gchrizZz/RTW/01_Projektmanagement/Structural Model Mohne.pdf

Motoren

MPU/ Gyroskope/
Ultraschallsensor/
Kamera

Arduino Uno /
Rasbery Pi

Servoelemente
(Vorwärtsbewegung) Motorleistung
steuert | Kommuniziert
kontrolliert | überwacht | kontrolliert
