gchrizZz/RTW/01_Projektmanagement/Aufgabenstellung_Uebung1.pdf

# Mars Explorer

Thomas Schmiedinger
thomas.schmiedinger@fh-kufstein.ac.at
13. Januar 2018

1

## 1 Embedded Systems UE - Raspberry Pi und Kameramodul

Als Teil des Projekts Mars Explorer soll im Rahmen der LV Embedded Systems UE die Hardware-Basis, der Raspberry Pi 3 und das Kameramodul, kennenge-
lernt werden. Der Raspberry Pi bildet das Ruckgrat f ¨ | ur den Mars Explorer. Aus ¨
diesem Grund beschäftigt sich die erste Einheit ausschließlich mit den Basics des Systems.

### 1.1 Ziel der Ubung ¨

Ziel der Ubung ist die erfolgreiche Inbetriebnahme des Raspberry Pi 3. Dazu ¨ zählt der Hardware-Aufbau, die Installation eines Betriebssystems, Anbindung an das Internet und ein abschließendes Systemupdate. Ein weiteres Ziel der
Ubung ist die Inbetriebnahme des Kameramoduls. Dazu z ¨ | ählt der physische
Anschluss an den Raspberry Pi, die Konfiguration des Raspberry Pis sowie die Ansteuerung der Kamera mit einem Python-Programm.

### 1.2 Beurteilung der Ubung ¨

Mithilfe des Raspberry Pis und der Kamera soll ein Bild sowie eine kurze Videosequenz (ca. 5sec) aufgenommen und gespeichert werden. Beide Files werden als zip-Ordner in Moodle hochgeladen.

### 1.3 Aufgabenstellung

### 1.3.1 Aufbau der Hardware

1. Entfernen Sie die Schutzfolie auf beiden Seiten der Plexiglas Grundplatte.
2. Offnen Sie die Box des Raspberry Pi 3 (Achten Sie auf die beigelegte ¨ SD-Karte).
3. Setzen Sie die SD Karte in den Raspberry Pi 3 ein.

2

4. Montieren Sie den Raspberry Pi auf der Grundplatte. Verwenden Sie dazu die kleinen der beigelegten Schrauben.
5. Befestigen Sie das Breadboard auf der Grundplatte.
6. Schließen Sie USB Tastatur und USB Maus an den Raspberry Pi 3 an. Verwenden Sie dazu die Eingabegeräte an den Stand-PCs.
7. Schließen Sie das HDMI Kabel an den Raspberry Pi 3 an.
8. Schließen Sie das USB Netzteil am Raspberry Pi 3 an.
9. Verbinden Sie das USB Netzteil mit der Stromversorgung.

### 1.3.2 Installation des Betriebssystems

Nachfolgend sind grob die einzelnen Schritte zur Installation angefuhrt. Eine ¨
gute Quelle fur weitere Informationen ist auf der Homepage der ¨ | Raspberry
Foundation (https://www.raspberrypi.org/) zu finden. Beim ersten Hochfahren mit NOOBS erscheint ein Auswahlbildschirm. Hier können Sie auswählen, welches Betriebssystem Sie auf dem Raspberry Pi 3 installieren wollen.
1. Wählen Sie das Betriebssystem Raspbian. (http://raspbian.org/) Fur das weitere Projekt steht ¨ Ihnen die Wahl des Betriebssystems fur den Raspberry Pi 3 frei. Eine gute ¨
Ubersicht zu den unterschiedlichen Systemen finden Sie ¨ | hier. (https://raspberrypi.stackexchange.com/questions/534/definitive-list-of-operating-systems)
2. Das Betriebssystem wird installiert.
3. Stellen Sie eine Internetverbindung her. Verbinden Sie dazu das Netzwerkkabel mit dem Raspberry Pi oder stellen Sie via Wlan eine Verbindung mit dem Internet her (Wifi-Netzwerk FH-Gast).
4. Nach erfolgter Installation wird das Betriebssystem auf den aktuellen Stand gebracht.
5. Offnen Sie das Terminal. ¨
6. Fuhren Sie ein Update aus. Geben Sie den Befehl ¨ | sudo apt-get update
in das Terminal ein und bestätigen Sie mit Enter.
7. Fuhren Sie nun ein Upgrade durch. Der Befehl lautet ¨ | sudo apt-get dist-upgrade.
Das System ist nun auf aktuellen Stand.

3

### 1.3.3 Kamera anschließen

1. Fahren Sie den Rapsberry Pi 3 herunter und kappen Sie die Verbindung zur Stromversorgung.
2. Verbinden Sie die Kamera mit dem Raspberry Pi 3.
3. Starten Sie den Raspberry Pi 3.
4. Offnen Sie das Programm ¨ | Raspberry Pi Configuration Tool. Sie fin-
den dieses im Menupunkt ¨ | Preferences.
5. Aktivieren Sie die Kamera.
6. Starten Sie den Raspberry Pi 3 neu.

### 1.3.4 Kameravorschau starten

1. Starten Sie unter Programming das Programm Python 3.
2. Erstellen Sie eine neue Datei und speichern Sie diese.
3. Erstellen Sie folgenden Code:

from picamera import PiCamera
from time import s l e e p

camera = PiCamera ( )

camera . s t a r t p r e v i e w ( ) s l e e p ( 1 0 )
camera . s t o p p r e vi e w ( )
4. Speichern Sie die Datei und starten Sie das Programm (F5).
5. Sollte das Bild auf dem Kopf stehen, können Sie die Ausrichtung des Bildes ändern. Verwenden Sie dazu folgenden Code:

from picamera import PiCamera
from time import s l e e p

camera = PiCamera ( )

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

4

Das Bild kann um 90, 180 oder 270 Grad gedreht werden.

6. Testen sie die Transparenz Einstellungen der Kamera. Verwenden Sie dazu folgenden Code:

from picamera import PiCamera
from time import s l e e p

camera = PiCamera ( )

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

Der Wert fur alpha bestimmt die Transparenz und kann zwischen 0 und ¨ 255 geändert werden.

### 1.3.5 Bild aufnehmen und abspeichern

1. Nehmen Sie mit der Kamera ein Bild auf und speichern Sie diese ab.
2. Fuhren Sie dazu folgendes Programm aus: ¨

from picamera import PiCamera
from time import s l e e p

camera = PiCamera ( )

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

Die Wartezeit von 2 Sekunden ist notwendig, damit sich der Kamerasensor auf die Lichtverhältnisse einstellen kann.

3. Offnen Sie das Foto. ¨
4. Adaptieren Sie das Programm um 5 Bilder in Serie aufzunehmen.

### 1.3.6 Video aufnehmen und abspeichern

1. Nehmen Sie mit der Kamera ein kurzes Video auf und speichern Sie diese ab.

5

2. Fuhren Sie dazu folgendes Programm aus: ¨

from picamera import PiCamera from time import s l e e p

camera = PiCamera ( )

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

6

## 2 Hinweise

### 2.1 Remote-Zugriff auf Raspberry Pi

Es besteht die Möglichkeit, mittles SSH Verbindung auf den Raspberry Pi zuzugreifen. Eine Anleitung dazu finden auf der Homepage der Raspberry Pi Foundation. (https://www.raspberrypi.org/documentation/remote-access/ssh/) Dies funktioniert nur nach Installation der Betriebssoftware.

Nachteil der PuTTY Lösung ist, dass es einen Zugriff auf die Kommandozeile gibt. Um auch die Oberfläche zu starten, folgen Sie der Anleitung. (http://42bots.com/tutorials/access-raspberry-pi-terminal-and-desktop-remotely-with-ssh-and-vnc/) Prinzipiell handelt es sich dabei um eine Erweiterung der SSH Anbindung um somit auch den Desktop des Raspberry Pis via remote anzeigen zu können.

Prinzipiell ist eine SSH-Anbindung ausreichend. Mithilfe von Kommandozeilen Befehlen ist es möglich, Dateien zu verwalten (z.B. Ordnerstruktur erstellen, Dateien verschieben etc.). Einen guten Uberblick der meisten Linux Befehle ¨ finden Sie hier. (https://www.raspberrypi.org/documentation/linux/usage/commands.md)

### 2.2 Ansteuerung von Sensoren und Aktoren - GPIO

Der Raspberry Pi 3 besitzt ein Interface uber welchem mit Sensoren und Aktoren ¨ kommuniziert werden kann. Die GPIO Pins besitzen unterschiedliche Funktionalitäten. Die Ansteuerung der Pins ist in diesem Tutorial (https://tutorials-raspberrypi.de/raspberry-pi-gpio-erklaerung-beginner-programmierung-lernen/) gut erklärt. Fur die ¨ vorhandene Sensoren finden Sie hier (http://sensorkit.joy-it.net/index.php?title=Hauptseite) Beispielprogramme.

### 2.3 Unified Modelling Language fur Raspberry Pi ¨

Mit folgenden Befehl in der Kommandozeile können Sie Umbrella auf Ihrem Raspberry Pi 3 installieren:

ssudo apt-get install umbrello

7

### 2.4 Informationen zur Picamera

Die Software der Kamerasteuerung bietet weitere Funktionalität hinsichtlich
Aufnahmemodi. Weiterfuhrende Informationen dazu finden Sie auf auf ¨ | Picame-
ra. (https://picamera.readthedocs.io/en/release-1.13/)

### 2.5 Informationen zu Objekterkennung

Spannend wird das Projekt hinsichtlich Objekterkennung. Der Raspberry Pi 3 in Kombination mit einer Kamera bietet die Möglichkeit, dies umzusetzen. Eine Möglichkeit dazu, bietet die Umgebung OpenCV. (https://opencv.org/) Von OpenCV finden sich einige Tutorials im Netz, wie auch dieses (https://docs.opencv.org/master/d2/d64/tutorial_table_of_content_objdetect.html) in welchen die Erkennung von Objekten gezeigt wird. Informationen dazu finden Sie auf der Homepage von
pyimagesearch. (https://www.pyimagesearch.com/start-here-learn-computer-vision-opencv/) Eine Installationsanleitung fur OpenCV findet sich ¨ | hier. (https://tutorials-raspberrypi.de/opencv-auf-dem-raspberry-pi-installieren/)
Eine weitere Inspirationsquelle fur Objekterkennung bietet die Freeware ¨ | YOLO. (https://pjreddie.com/darknet/yolo/)
Die Funktionalität dieses Programm wurde von Joseph Redmon im Rahmen eines TED-Talks (https://www.ted.com/talks/joseph_redmon_how_a_computer_learns_to_recognize_objects_instantly/up-next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) eindrucksvoll demonstriert.

8
