gchrizZz/RTW/04_Elektrik/Elektrik.pptx

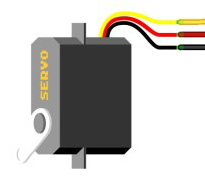
[picture p71: figure]
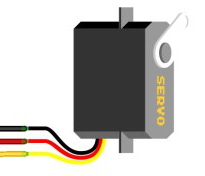
[picture p72: figure]
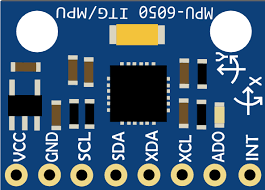
[picture p73: figure]
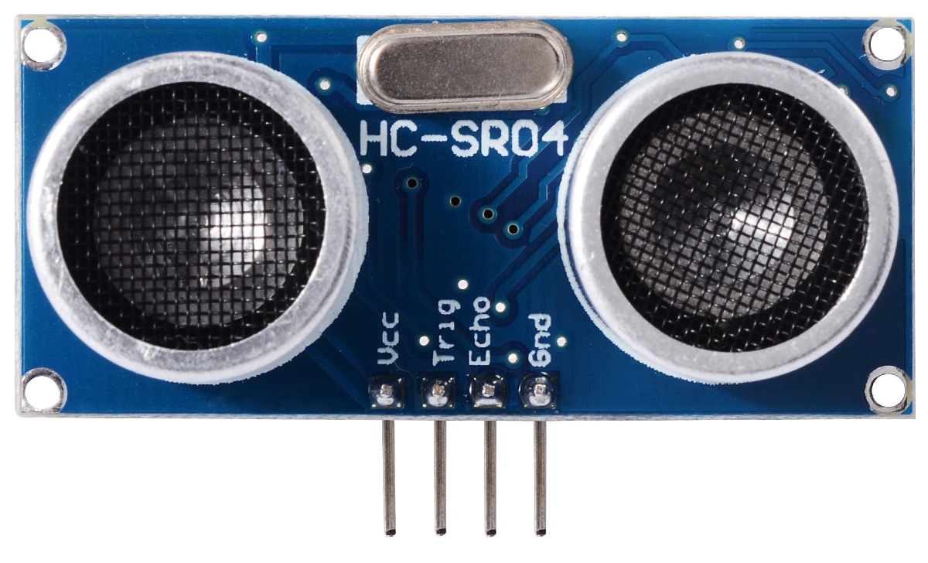
[picture p74: figure]
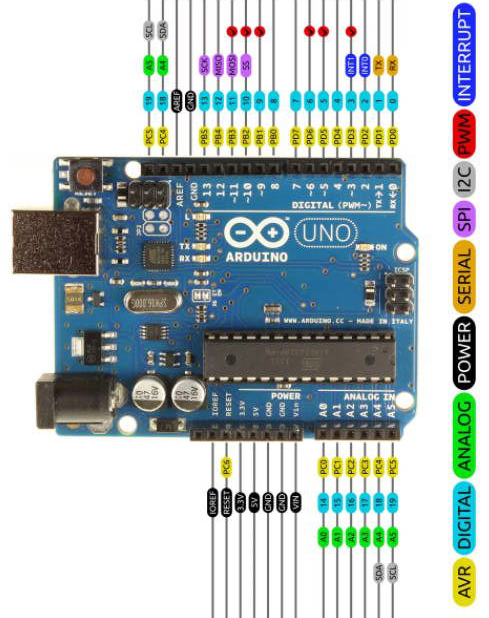
[picture p75: figure]
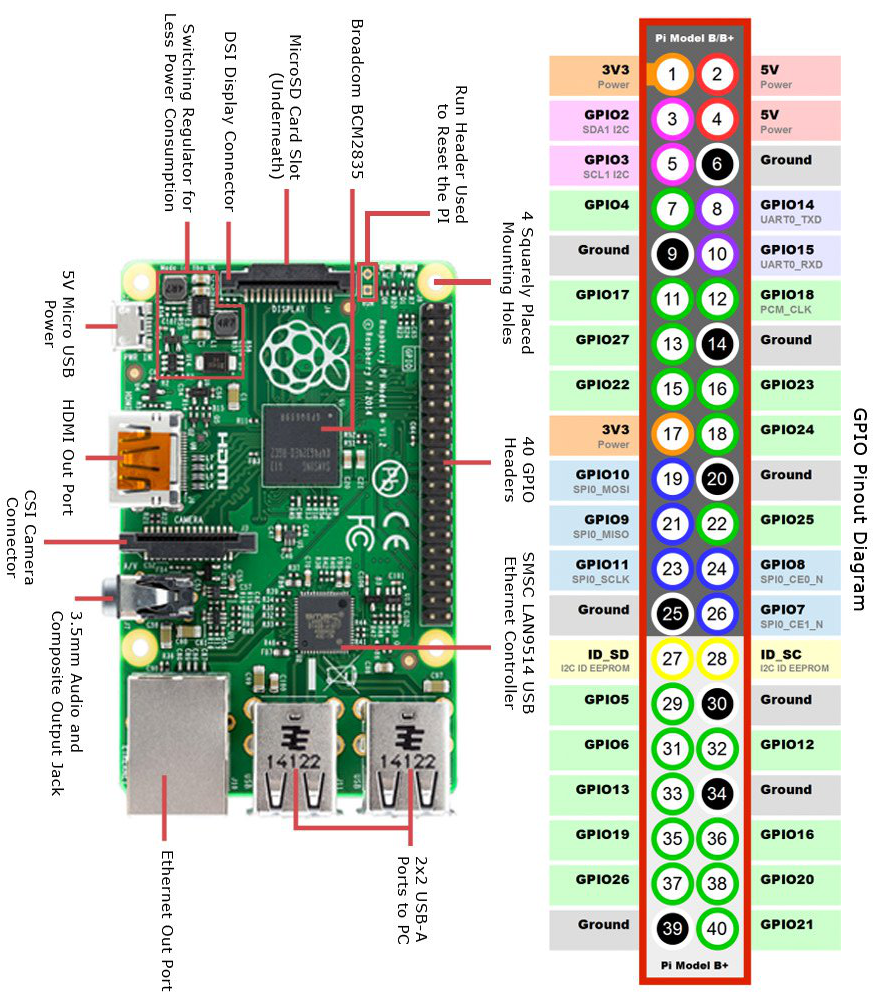
[picture p76: figure]
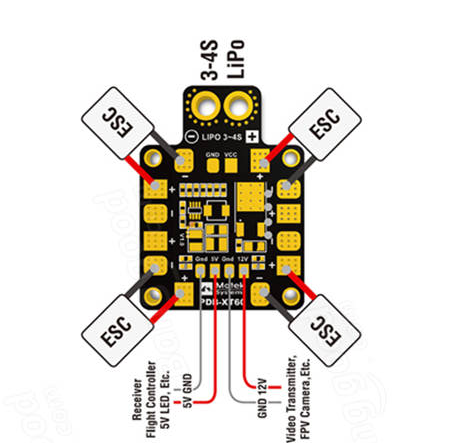
[picture p77: figure]
