gchrizZz/RTW/01_Projektmanagement/Assignment 5 - Project Managements Methods - ACC.pptx

## Smart Produkt Solutions Assignment 5 – Project Management Methods SPS bbM, WS 2017/18

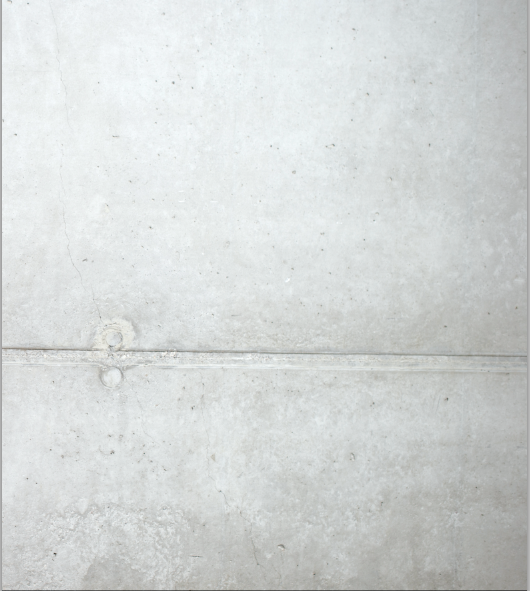
[picture p78: figure]
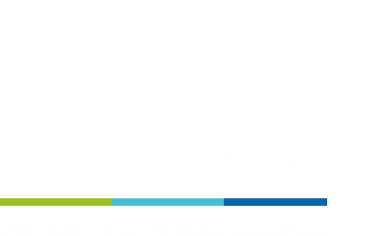
[picture p79: figure]

## Slide 2

Project Management Methods - "Mars Expedition"

Assignment 5 – Project Management Methods
Planning vehicle for „Mars Expedition“
Anna Duregger,
Christoph Jungwirth,
Christian Gruber

## Project use case

Distribution of roles
  - Project manager and deputy project manager
  - Head of construction
  - Head of computer engineering
  - Head of electronic engineering
  - Decision maker
  - Responsibility

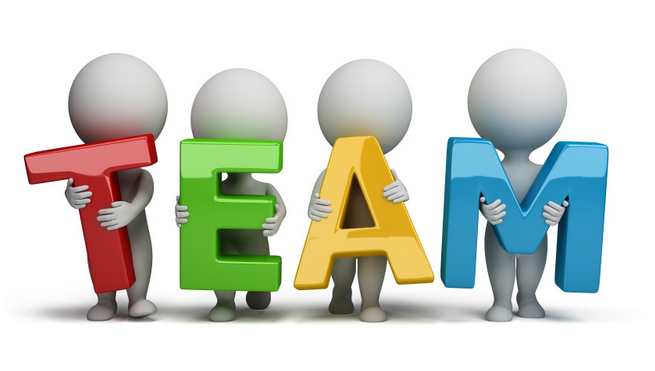
[picture p80: figure]

Quelle: http://www.flensburger-budo-club.de/attachments/Image/team.jpg?template=generic

## Project use case

Phase planning
  - Conception phase
  - Define and Planning phase
  - Execution Phase
  - Closing Phase (Mars Landing)
  - Structure
  - Set up activities
  - Work step by step

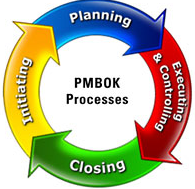
[picture p81: figure]

Source: http://www.mpmm.com/images/pmbok-processes.jpg

## Project use case

Milestones
  - 1st: Structure, basic concept, distribution of roles
  - 2nd: Prototyping of our Mohne
  - 3rd: Optimization for our finalisation phase
  - Control project progression
  - Relief project planning

Quelle: http://laoblogger.com/images/milestone-clipart-10.jpg

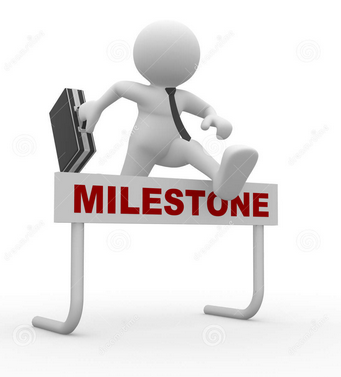
[picture p82: figure]

## Project at a glance

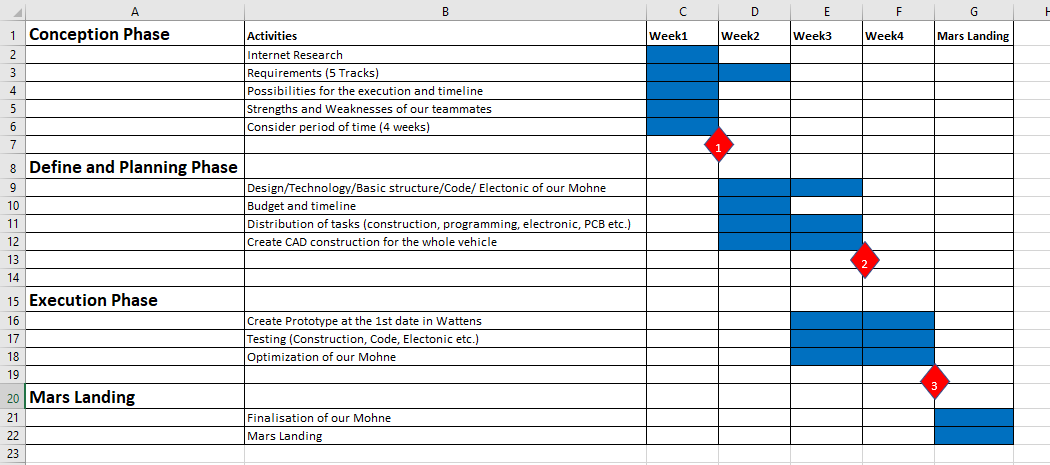
[picture p83: figure]

## Project supporting tools

GitHub
- Used as a Collaboration Tool for the Project
- Separate the Tasks regarding the project phases
- In addition to the project plan → more clearly & detailed
Templates (based on Excel)
- Project owner Requirements (Tasks for the Robot)
- Team Member Structure (Who is Who?)
- Risk analysis (for the Robot)
- Technical Requirements (Construction)

## Risk evaluation of the Project

- Evaluating potential Risks of the Project regarding the customer requirements
- Create controlling tools for the detected risks
- Finding solutions for the come out risks
- Discriminate between project risks and standard risks

Standard risks | Project risks
Competing goals | Technical Issues
Project environment | Time Table / Delivery Schedule
Stakeholder | Customer Requiremants

## Traditional vs. Agile Methods

Traditional project management:
What‘s the overall plan and conditions - in our Project?

- Specification list
- Risk analysis
- Define goal

Initiation

- Work off Workpackages
- Document the progress

Execution

- Work off Workpackages
- Document the progress

Closing

Planning

- Milestone plan
- Determine resources
- Define work packages

Monitoring & Control

- Control scope, progress, cost
- Readjust the project planning

## Traditional vs. Agile Methods

Traditional project management:
Goal of traditional project management - in our project?

TIME

COST

In our case:

QUALITY

QUALITY? – We will see

TIME

COST=Budget

SCOPE

SCOPE

## Traditional vs. Agile Methods

Agile project management:
Agile development in our project?

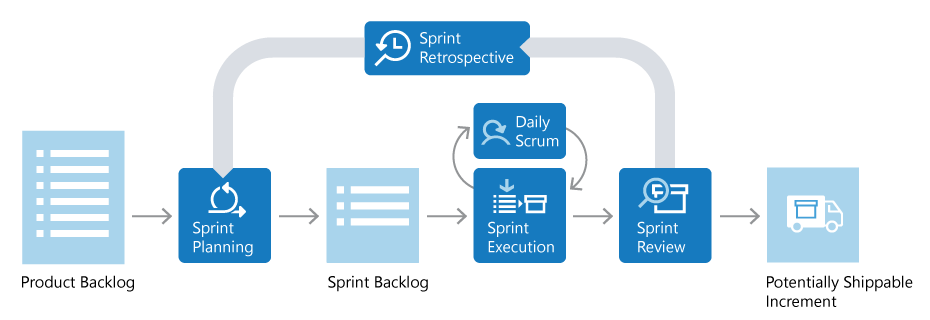
[picture p84: figure]

Daily communication via whatsapp and github
(for CAD and sourcecode)

Our „To Do“ on github

„In progress“ on github

Review with the complete team over all accomplished workpackages

Source: https://www.visualstudio.com/de/learn/what-is-scrum/?rr=https%3A%2F%2Fwww.google.de%2F

## Traditional vs. Agile Methods

Conclusion:

Traditional | Agile
Formal and hierarchical – straight forward | Informal, decisions are made in the entire team – loops possible
Anticipation: No changes during the project | Adaption: Embraces changes
Early planning and complete overview is key to success of the project | Fest reaction and adoption during the project is key to success

Overall planning

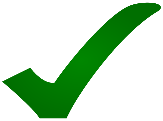
[picture p85: figure]

Development
