gchrizZz/RTW/01_Projektmanagement/Assignment 5 - Project Managements Methods_Christoph und Anna.pptx

## Smart Produkts & Solutions Assignment 5 – Project Management Methods SPS bbM, WS 2017/18


## Slide 2

Project Management Methods - "Mars Expedition"

HANDOUT NICHT VERGESSEN
Assignment 5 – Project Management Methods
Planning vehicle for „Mars Expedition“
Anna Duregger,
Christoph Jungwirth,
Christian Gruber

## Agenda

1. Project use case
2. Project at a glance
3. Project supporting tools
4. Risk evaluation of the Project
5. Traditional vs. Agil Methods

## Project use case

Phase planning
  - Conception phase
  - Define and Planning phase
  - Execution Phase
  - Mars Landing
  - Structure
  - Set up activities
  - Work step by step

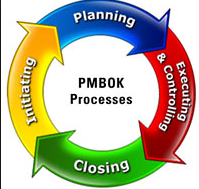
[picture p87: figure]

## Project use case

Milestones
  - 1st: structure, basic concept, distribution of roles
  - 2nd: prototyping our Mohne
  - 3rd: optimization for our finalisation phase
  - Control project progession
  - Relief project planning

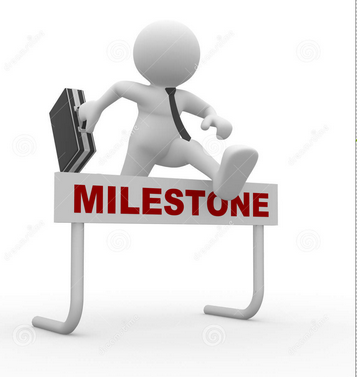
[picture p88: figure]

## Slide 6

Distribution of roles
  - Project Manager and Deputy Project Manager
  - Head of Construction
  - Head of computer engineering
  - Head of electronic engineering
  - Decision maker
  - Responsibility


## Project at a glance


## Project supporting tools

GitHub
- Used as a Collaboration Tool for the Project
- Separate the Tasks regarding the project phases
- In addition to the project plan → more clearly & detailed
Templates (based on Excel)
- Project owner Requirements (Tasks for the Robot)
- Team Member Structure (Who is Who?)
- Risk analysis (for the Robot)
- Technical Requirements (Construction)

## Risk evaluation of the Project

- Evaluating potential Risks of the Project regarding the customer requirements
- Create controlling tools for the detected risks
- Finding solutions for the come out risks
- Discriminate between project risks and standard risks

Standard risks | Project risks
Competing goals | Technical Issues
Project environment | Time Table / Delivery Schedule
Stakeholder | Customer Requiremants

## Traditional vs. Agil Methods
