gchrizZz/RTW/01_Projektmanagement/3dDrucker einstellungen.JPG

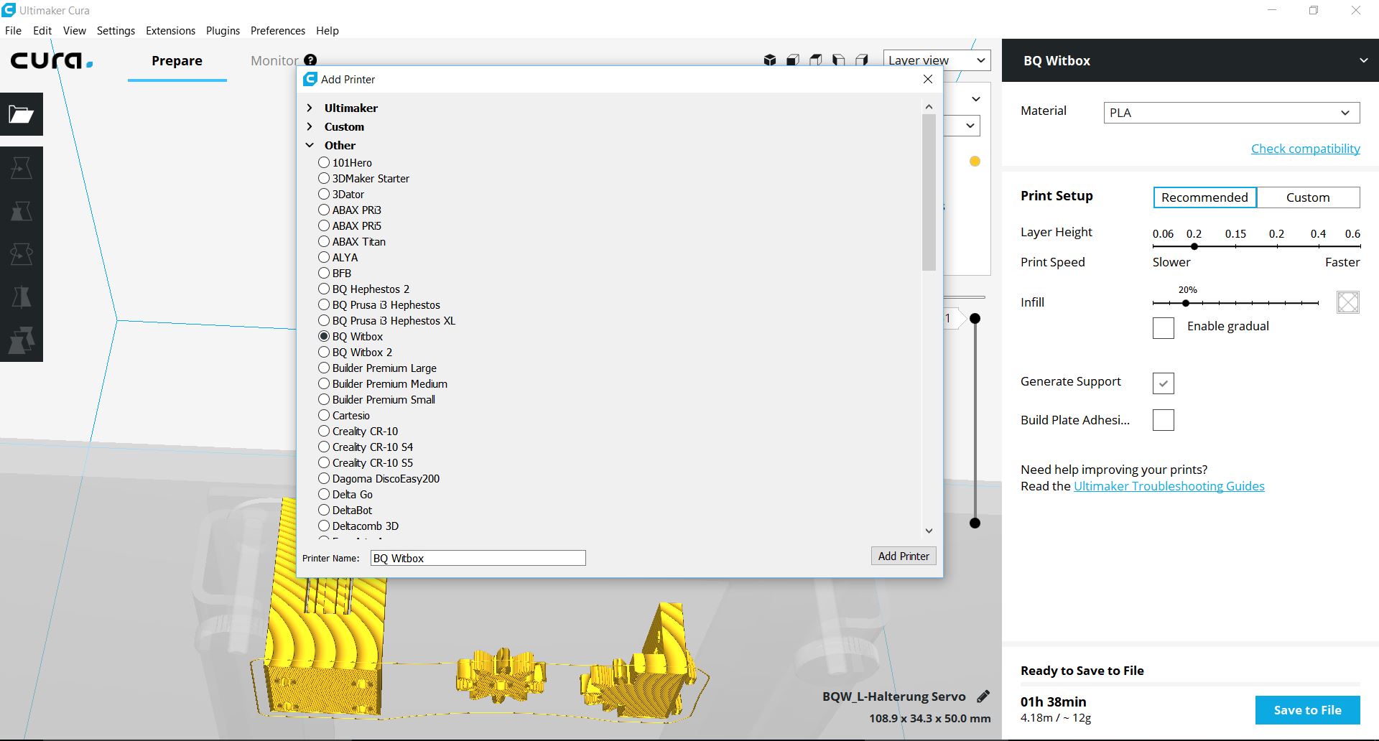
01_Projektmanagement/3dDrucker einstellungen.JPG
