gchrizZz/RTW/01_Projektmanagement/Bilder/IMG-20180123-WA0000.jpeg

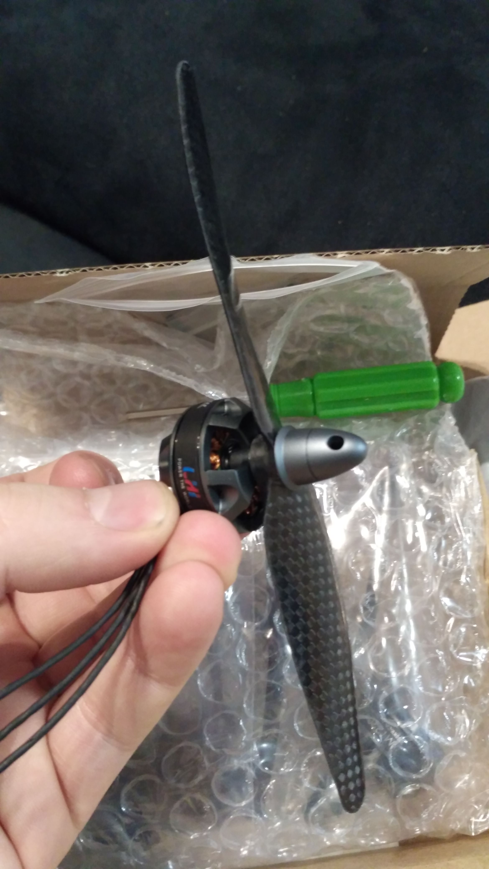
01_Projektmanagement/Bilder/IMG-20180123-WA0000.jpeg
