gchrizZz/RTW/01_Projektmanagement/Bilder/IMG-20180209-WA0006.jpeg

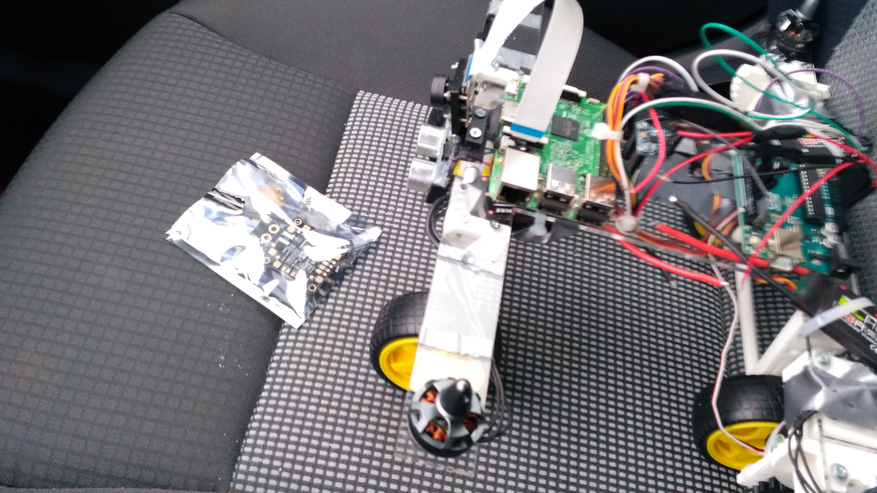
01_Projektmanagement/Bilder/IMG-20180209-WA0006.jpeg
