gchrizZz/RTW/01_Projektmanagement/Bilder/IMG-20180210-WA0005.jpg

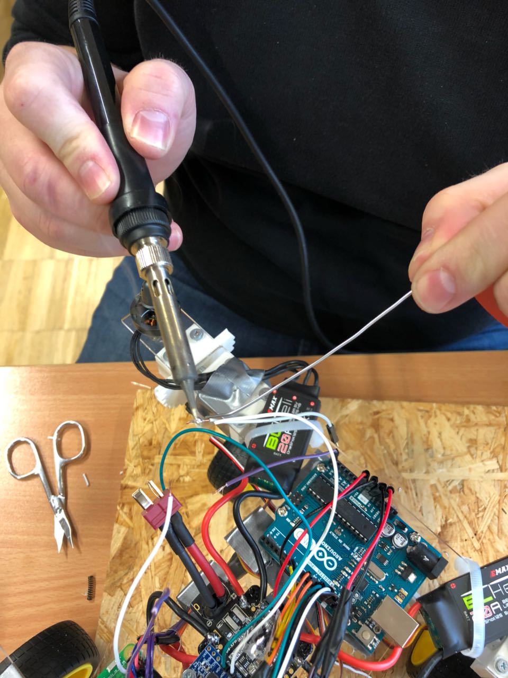
01_Projektmanagement/Bilder/IMG-20180210-WA0005.jpg
