gchrizZz/RTW/01_Projektmanagement/Bilder/IMG_20180129_200515.jpg

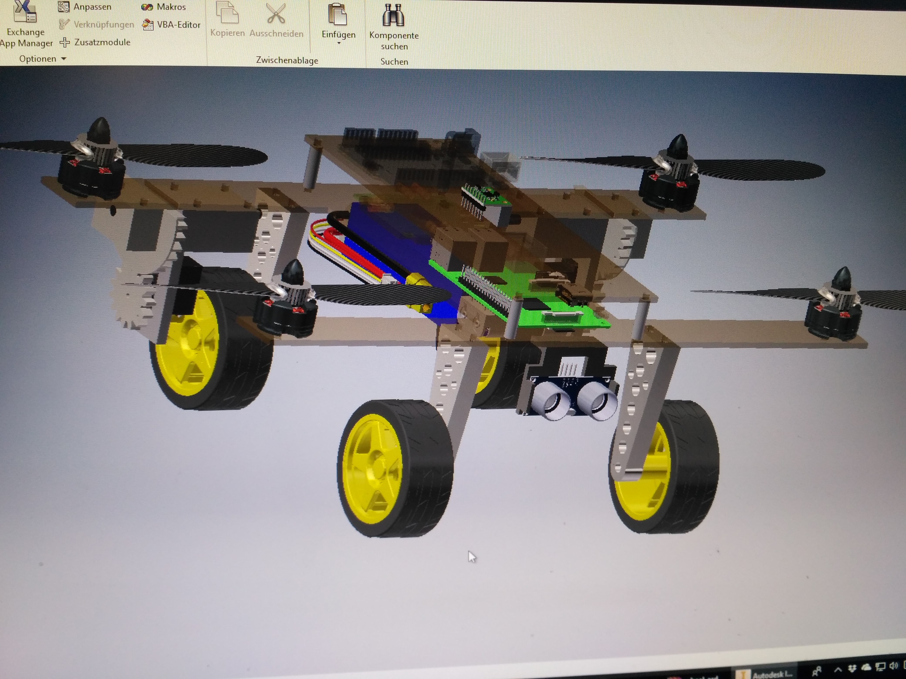
01_Projektmanagement/Bilder/IMG_20180129_200515.jpg
