gchrizZz/RTW/01_Projektmanagement/Bilder/PCB_monochromatic.jpeg

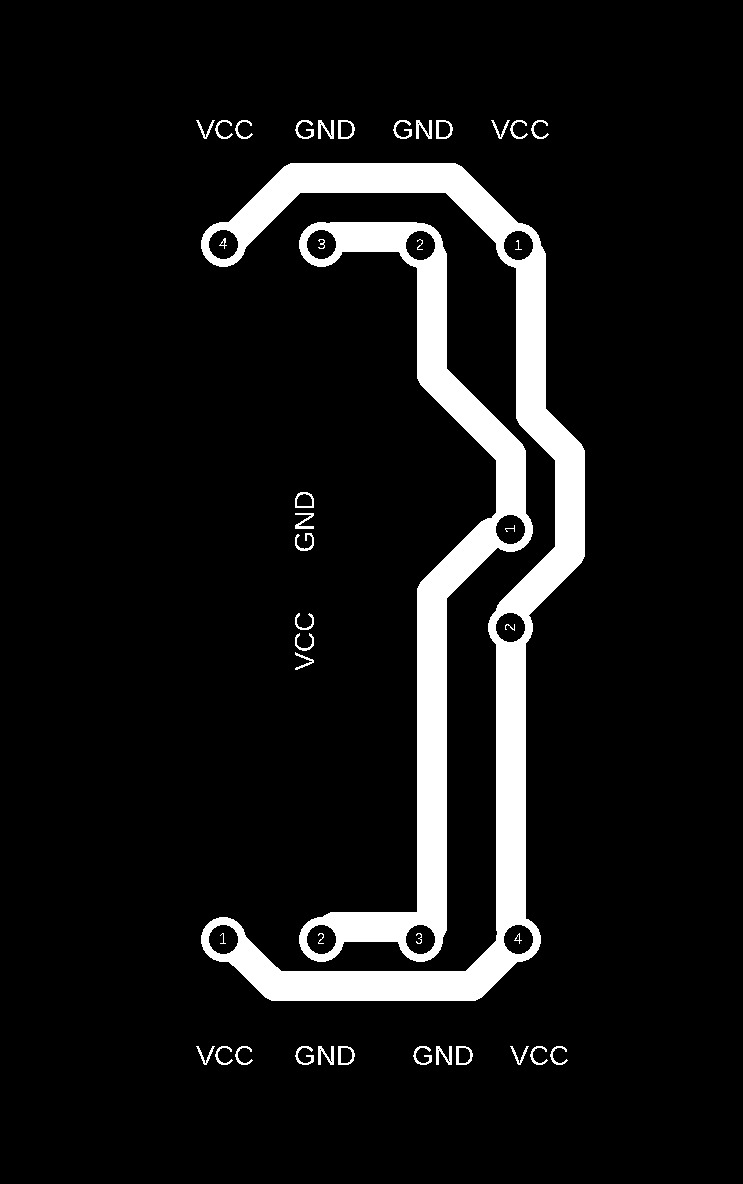
01_Projektmanagement/Bilder/PCB_monochromatic.jpeg
