gchrizZz/RTW/03_Konstruktion/2xAAA_ass.STEP

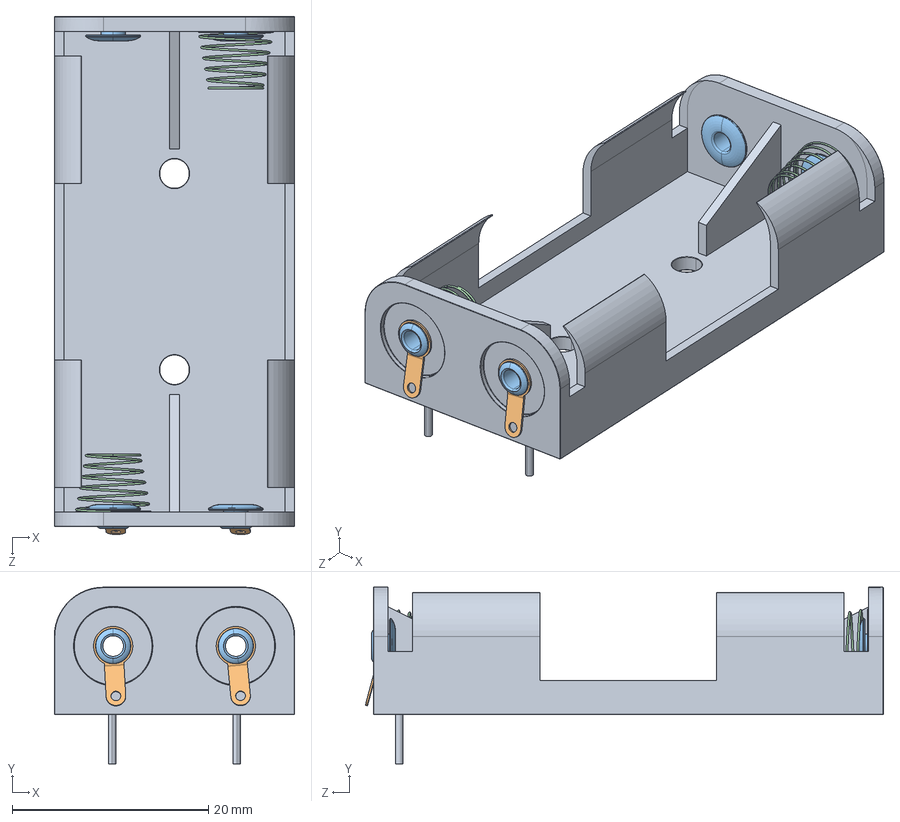
[picture p114: CAD file, 2018-01-30]
03_Konstruktion/2xAAA_ass.STEP
24.5 x 18.0 x 52.8 mm
battery holder 2 x AAA
wtyczka_Domyslna x 2
wstawka_Domyslna x 4
sprezyna_Domyslna x 2
