gchrizZz/RTW/03_Konstruktion/28-2-2013-002 - ESC 3-pin connector.SLDPRT

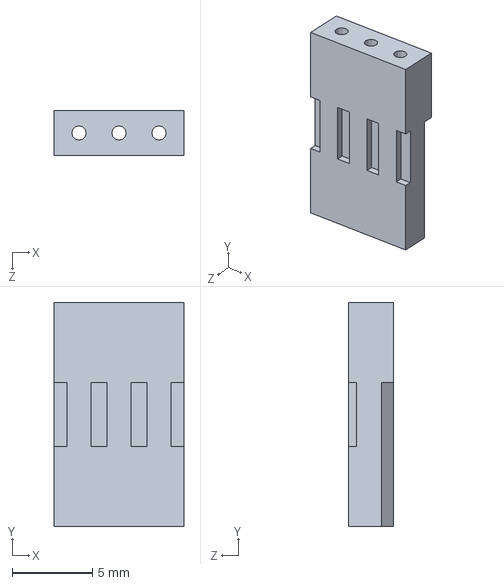
[picture p115: CAD file, 2018-01-30]
03_Konstruktion/28-2-2013-002 - ESC 3-pin connector.SLDPRT
8.10 x 14.0 x 2.80 mm
