gchrizZz/RTW/03_Konstruktion/Exporte/Abstandhalter_MPU.stl

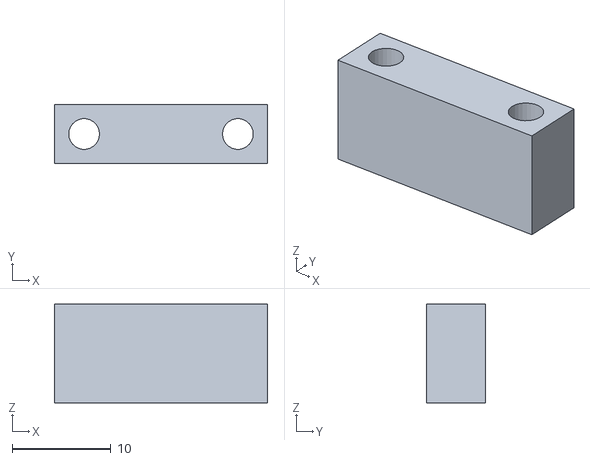
[picture p116: CAD file, 2018-01-30]
03_Konstruktion/Exporte/Abstandhalter_MPU.stl
21.6 x 6.00 x 10.0
