gchrizZz/RTW/03_Konstruktion/Exporte/kamera ut.stl

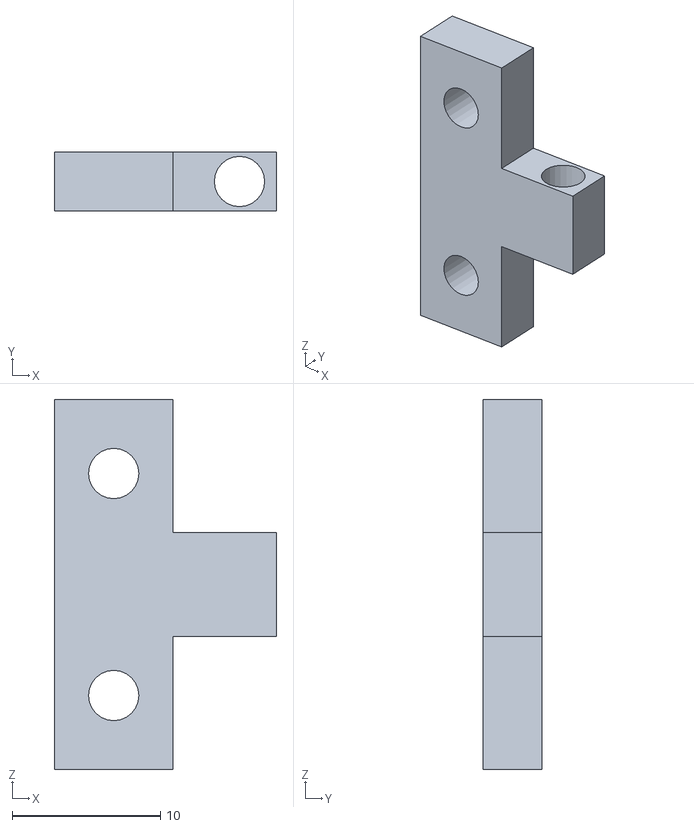
[picture p117: CAD file, 2018-01-30]
03_Konstruktion/Exporte/kamera ut.stl
15.0 x 4.00 x 25.0
