gchrizZz/RTW/03_Konstruktion/Resistor black.SLDPRT

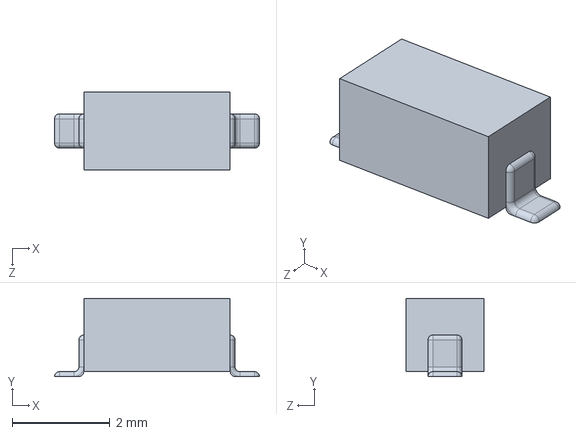
[picture p118: CAD file, 2018-01-20]
03_Konstruktion/Resistor black.SLDPRT
4.20 x 1.60 x 1.60 mm
