gchrizZz/RTW/03_Konstruktion/Base.SLDPRT

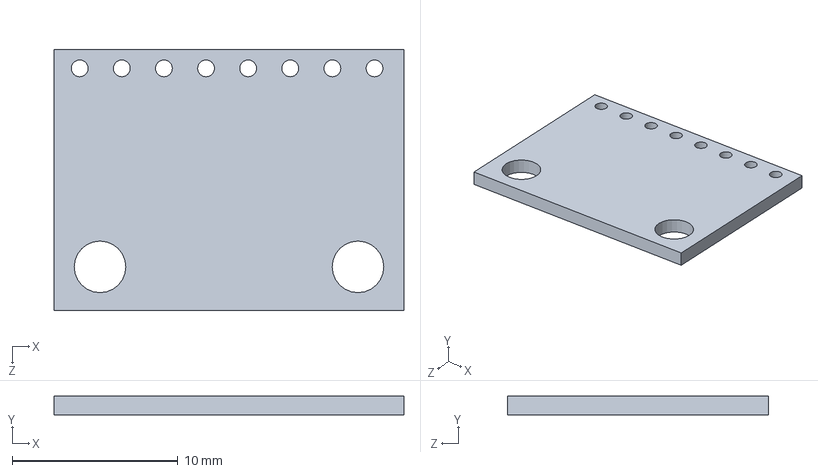
[picture p119: CAD file, 2018-01-20]
03_Konstruktion/Base.SLDPRT
21.1 x 1.14 x 15.7 mm
