gchrizZz/RTW/03_Konstruktion/MPU 6050 IMU.STEP

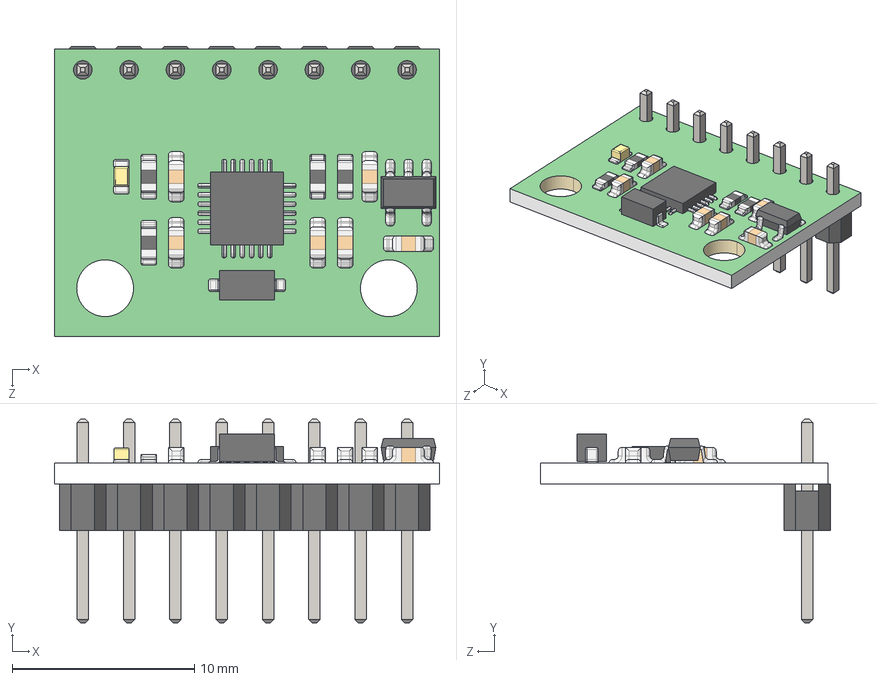
[picture p120: CAD file, 2018-01-20]
03_Konstruktion/MPU 6050 IMU.STEP
21.1 x 11.2 x 15.9 mm
Base
pin header x 8
sensor chip
S2NH chip
Resistor small x 6
Resistor small black x 4
Small LED
Resistor black
