gchrizZz/RTW/03_Konstruktion/Resistor small black.SLDPRT

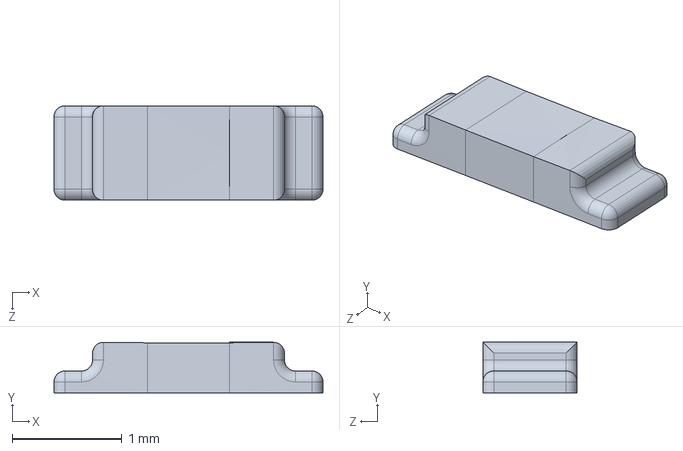
[picture p121: CAD file, 2018-01-20]
03_Konstruktion/Resistor small black.SLDPRT
2.45 x 0.46 x 0.86 mm
