gchrizZz/RTW/03_Konstruktion/sensor chip.SLDPRT

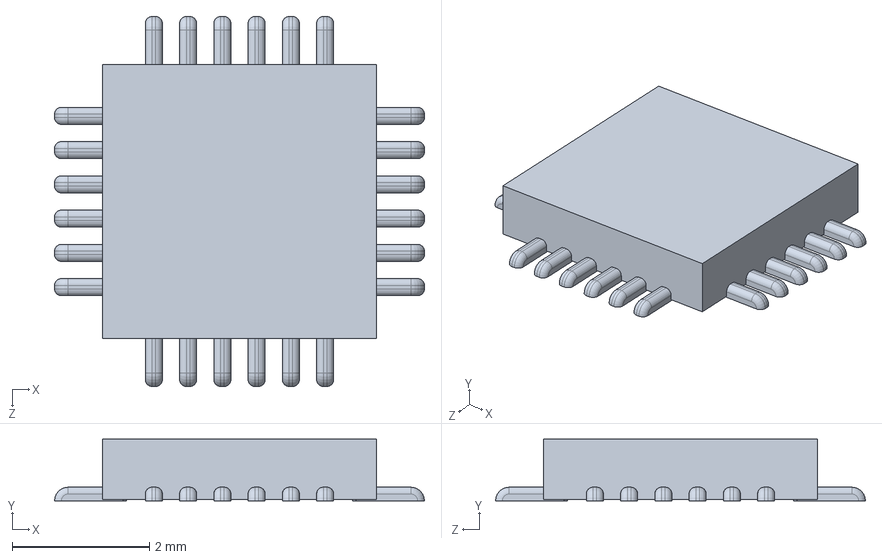
[picture p122: CAD file, 2018-01-20]
03_Konstruktion/sensor chip.SLDPRT
5.40 x 0.9 x 5.40 mm
