gchrizZz/RTW/03_Konstruktion/S2NH chip.SLDPRT

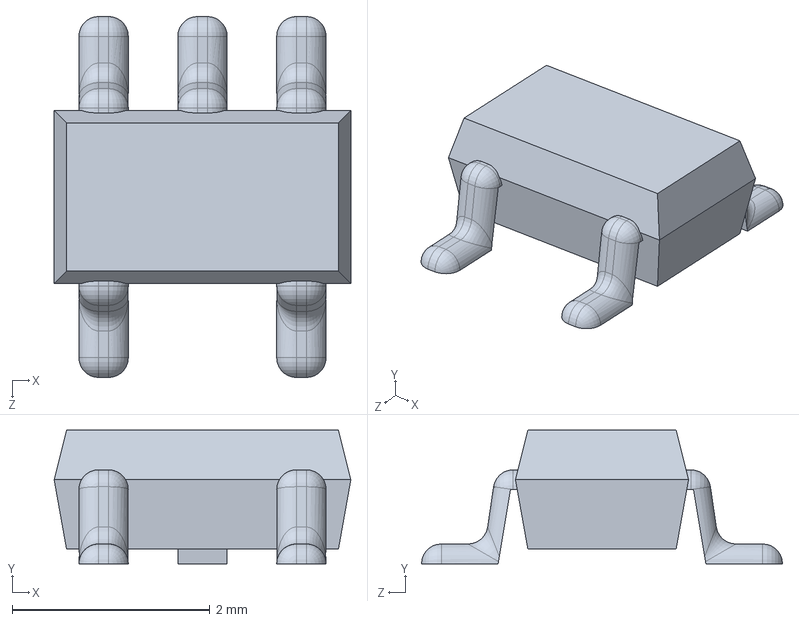
[picture p123: CAD file, 2018-01-20]
03_Konstruktion/S2NH chip.SLDPRT
3.00 x 1.35 x 3.65 mm
