gchrizZz/RTW/03_Konstruktion/Resistor small.SLDPRT

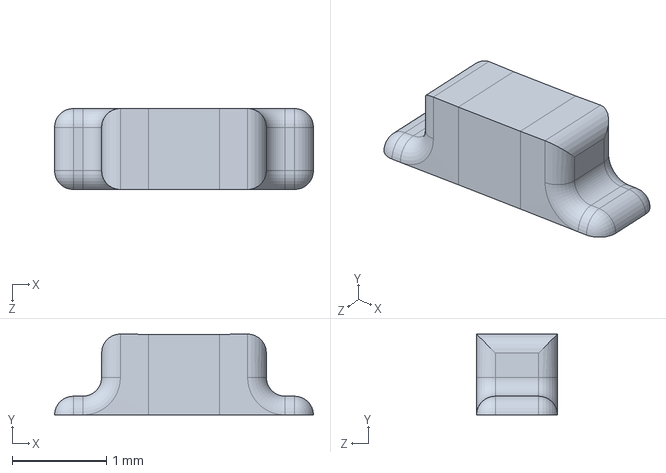
[picture p124: CAD file, 2018-01-20]
03_Konstruktion/Resistor small.SLDPRT
2.75 x 0.86 x 0.86 mm
