gchrizZz/RTW/03_Konstruktion/Small LED.SLDPRT

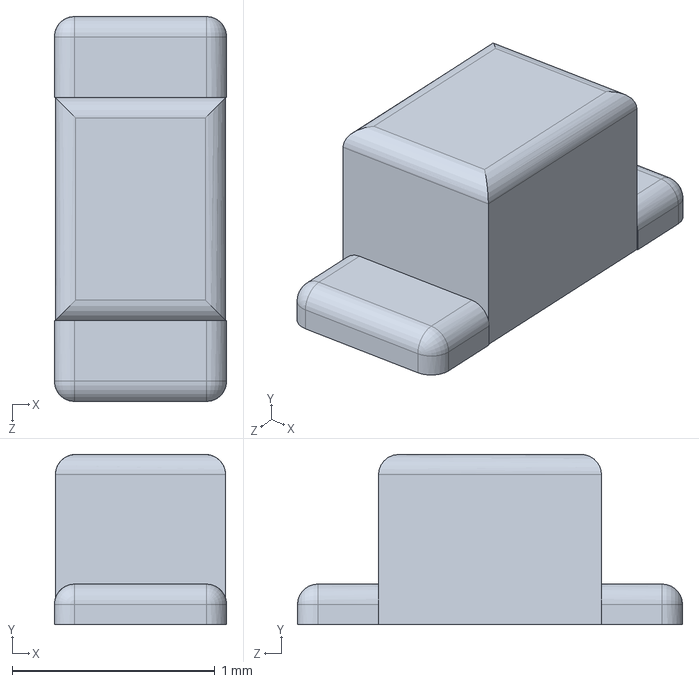
[picture p125: CAD file, 2018-01-20]
03_Konstruktion/Small LED.SLDPRT
0.85 x 0.84 x 1.90 mm
