gchrizZz/RTW/03_Konstruktion/pin header.SLDPRT

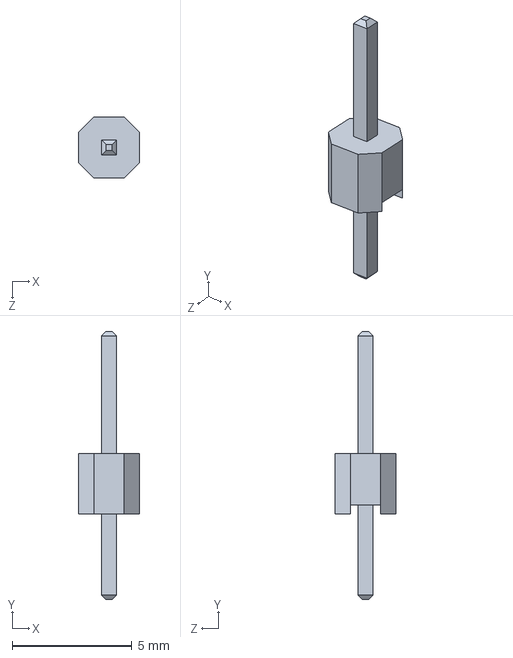
[picture p126: CAD file, 2018-01-20]
03_Konstruktion/pin header.SLDPRT
2.54 x 11.2 x 2.54 mm
