gchrizZz/RTW/02_Quellcode/Pi Programme/camDetect.py

# import the necessary packages
from picamera.array import PiRGBArray
from picamera import PiCamera
import time
import cv2
import math
import numpy as np

#dictionary of all contours
contours = {}
#array of edges of polygon
approx = []
#scale of the text
scale = 2

# initialize the camera and grab a reference to the raw camera capture
camera = PiCamera()
camera.resolution = (640, 480)
camera.framerate = 32
rawCapture = PiRGBArray(camera, size=(640, 480))
